H4D33D/arduino-vehicle-data-logger/graphs/graph-1-chevrolet/graph-1.jpg

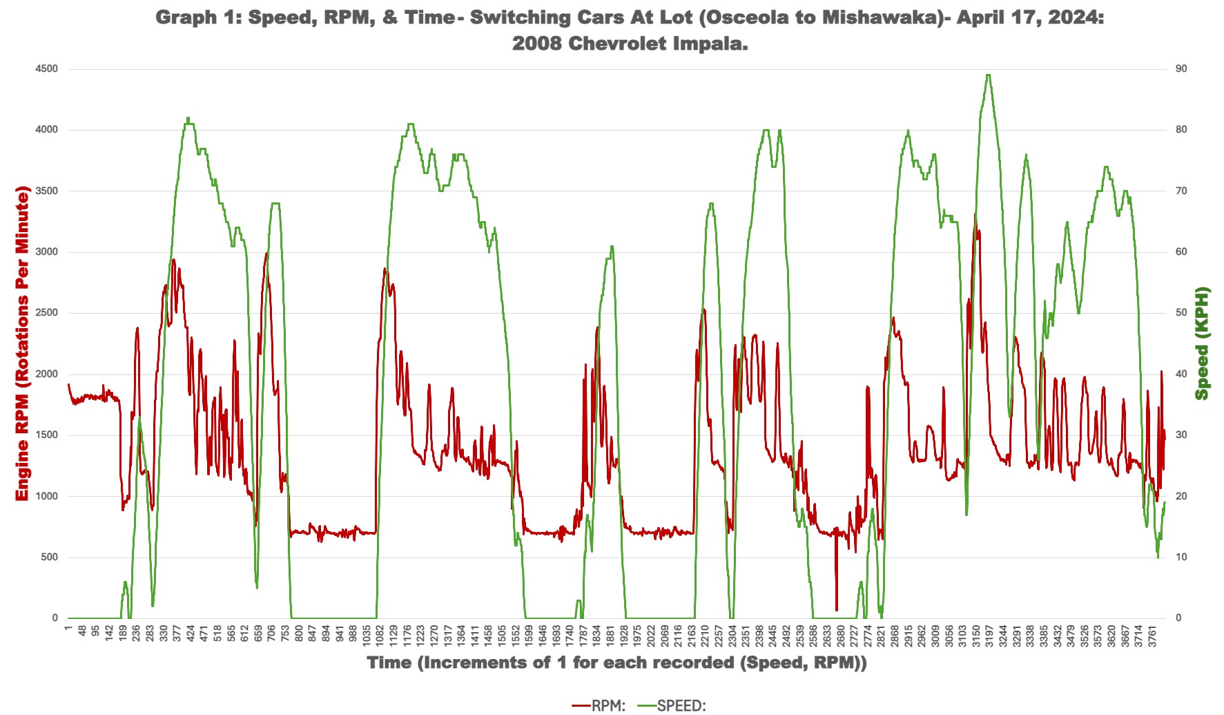
graphs/graph-1-chevrolet/graph-1.jpg
