H4D33D/arduino-vehicle-data-logger/graphs/graph-2-subaru/graph-2.jpg

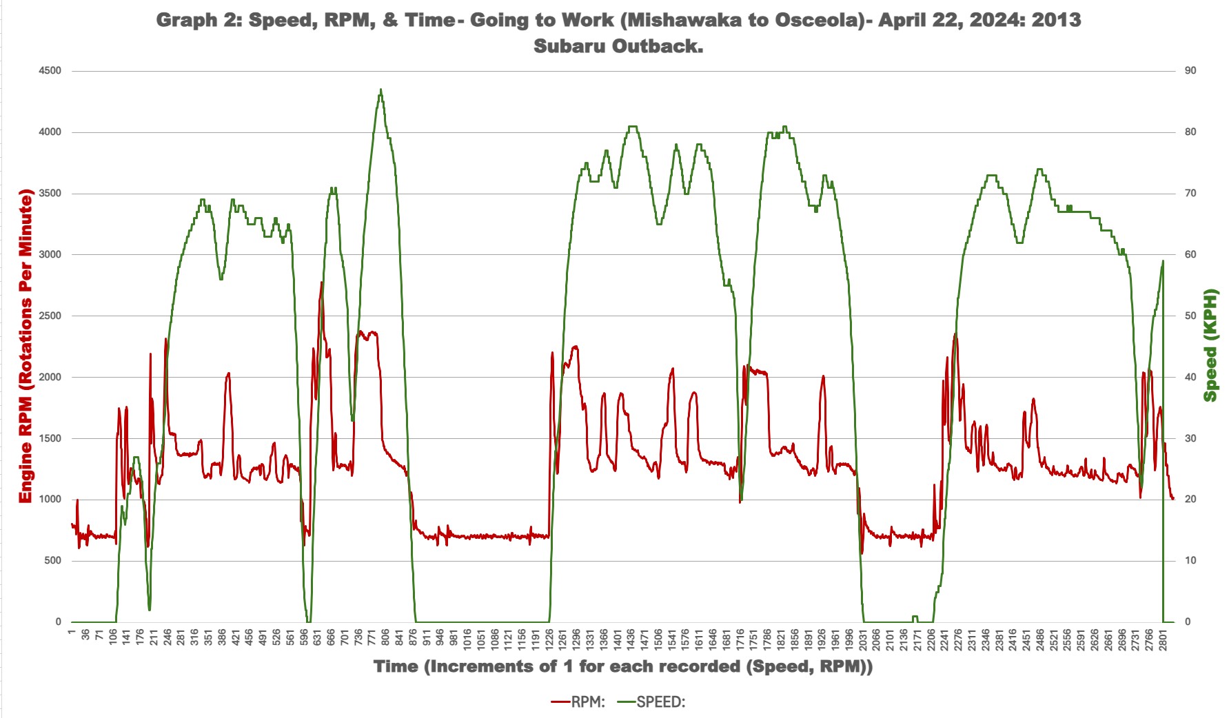
graphs/graph-2-subaru/graph-2.jpg
