H4D33D/arduino-vehicle-data-logger/graphs/graph-3-lexus/graph-3-annotated.jpg

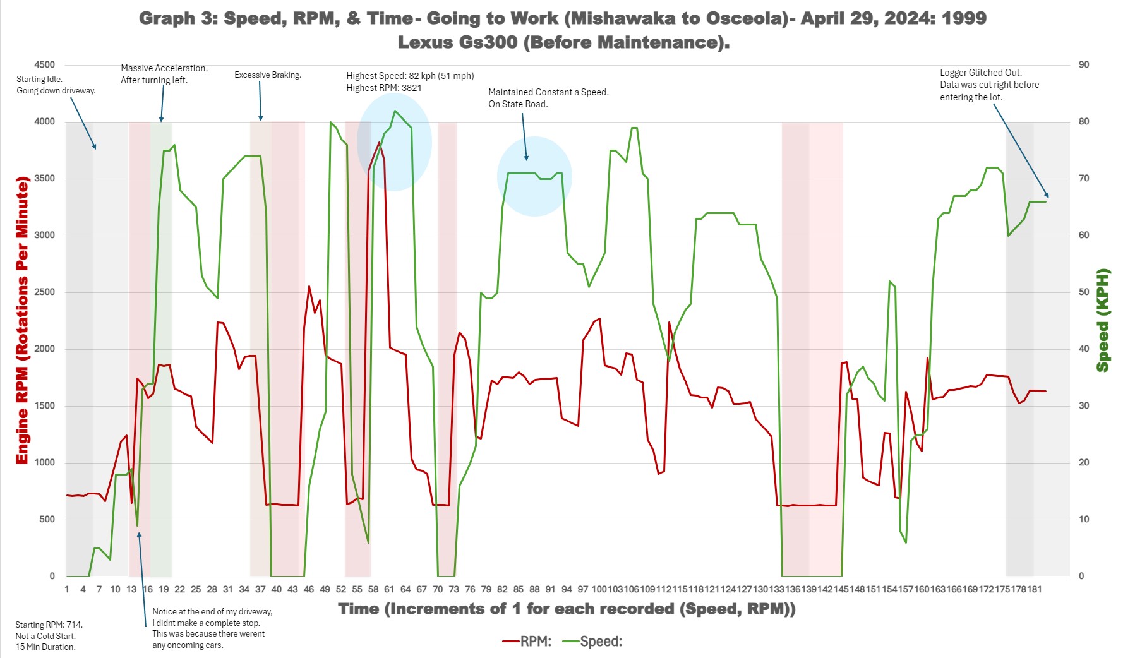
graphs/graph-3-lexus/graph-3-annotated.jpg
