H4D33D/arduino-vehicle-data-logger/graphs/graph-4-lexus/graph-4.jpg

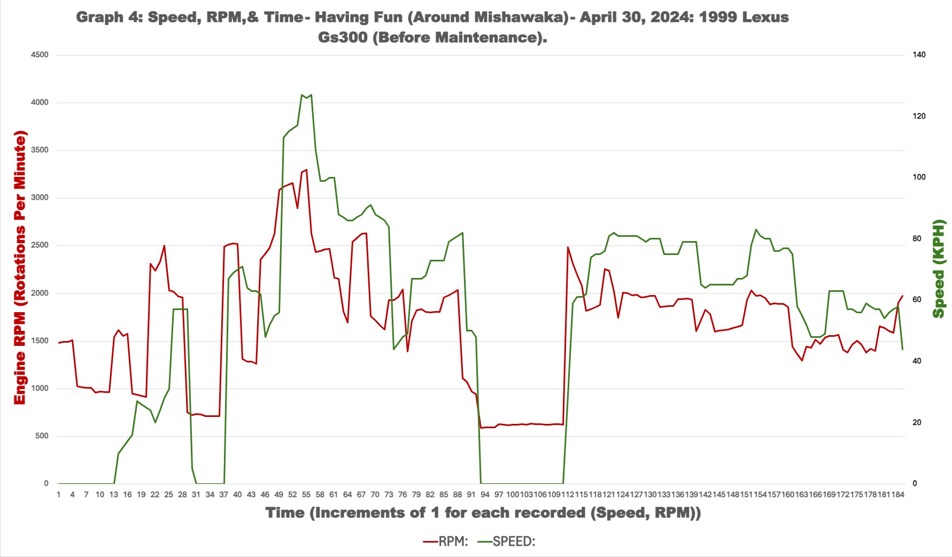
graphs/graph-4-lexus/graph-4.jpg
