H4D33D/arduino-vehicle-data-logger/images/obd2-logger-live-test-4.jpg

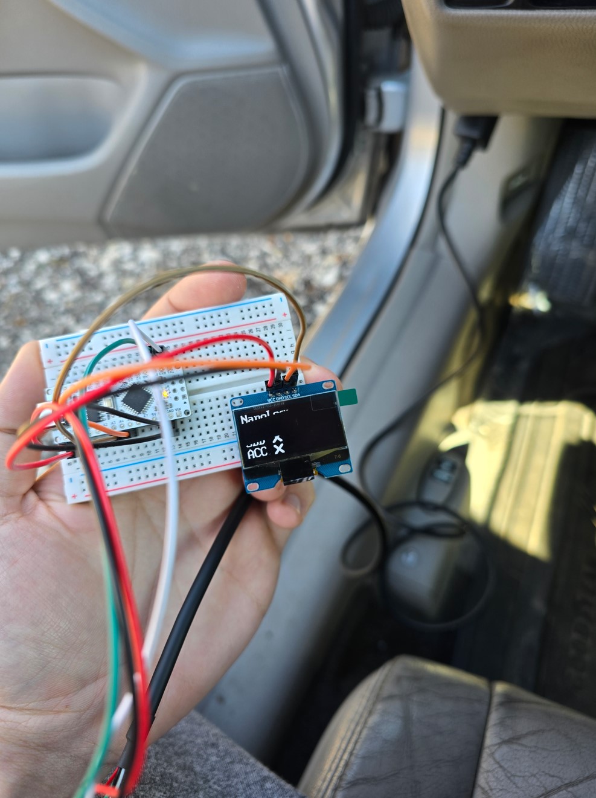
images/obd2-logger-live-test-4.jpg
